tianxiaogua/robot-handle-remote_hard/DOCUMENT/picture/1.png

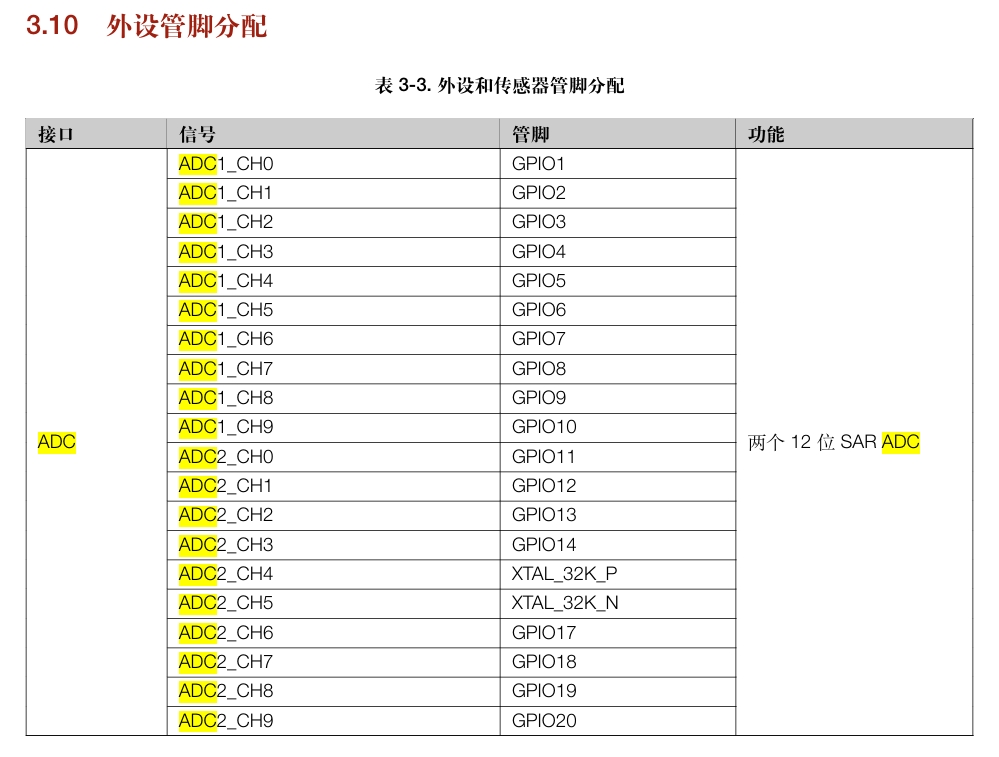
DOCUMENT/picture/1.png
