tianxiaogua/robot-handle-remote_hard/DOCUMENT/picture/2.png

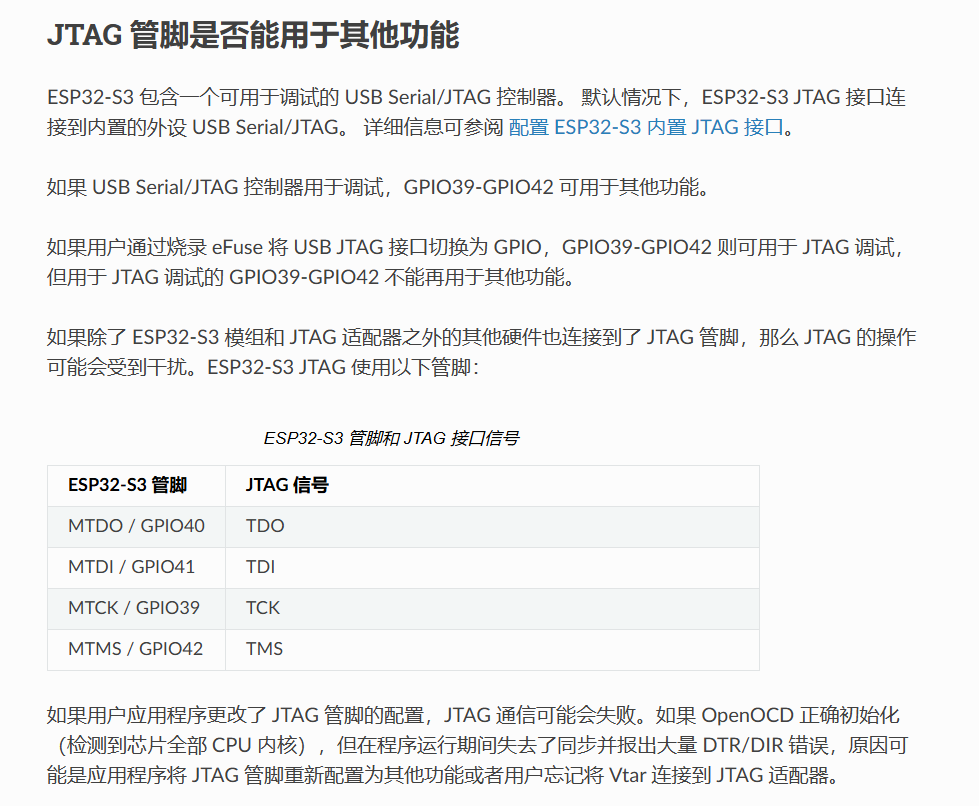
DOCUMENT/picture/2.png
